khaydarian/spla/blog/2020-02-15-a.md

# 2020-02-15

Started experimenting with KiCad, and drew some partial crummy schematics.  For
now, I'm mostly duplicating what the HX8K dev board and FT2232HL datasheets
do, with some minor exceptions:  The FT2232HL datasheet recommends an LC
(inductor-capacitor) filter on the VPHY and VPLL inputs, to stabilize the PLL
-- but the HX8K dev board just has some decoupling capacitors, so that's maybe
sufficient.

The bigger problem here is part selection.  The big parts are kinda simple in
concept, but figuring out which exactly to choose is hard.  I don't have
constraints on cost -- the parts are cheap enough in single quantities -- but I
don't have good intuition on how hard it is to manually solder these things.
THT (Through-hole) is easy; surface-mount is trickier.  Nate mention that
0603-sized resistor/capacitor parts are doable manually, but smaller is a pain.
TFQP parts are probably ok, because I can just dump a bunch of flux and solder
on, and wick off the rest.  For BGA, it's hard to do without a solder-reflow
oven, which is probably too expensive to be worth it for a one-off ($250 - $450).

Sockets are annoying for QFP-100 (20x30x20x30), and are obsolete and pretty
much impossible to get.  I could build a breakout board for the PPU chips, at
the cost of chunky traces for the high(er) speed signals.  Not great.  Probably
it's better to just solder the things directly to the board, and hope not to
screw it up too many times.

Desoldering the PPU chips might be a huge pain, but that's something to
discover the hard way.

I also probably want to be able to control the CRAM / SPI EEPROM programming
mode electronically (ie, without swapping jumpers all the time), and to
control the power to the PPU chips as well.  For this stuff it's harmless to
have jumpers to configure manually as well; I'll need to actually decide this
stuff and write it down.

The SRAM in most FPGAs is registered, so probably I can't use it to replace
the VRAM chips.  On the other hand, I'll get these for free with the SNES's, so
maybe it's wise to just use them.  Possibly I'll also want to be able to drive
these directly, and hold the PPU chips in reset.
