khaydarian/spla/blog/2020-02-14-b.md

# 2020-02-14

Found a good example of KiCad projects for Gameboy hardware: https://github.com/Gekkio/gb-hardware
