khaydarian/spla/reference/SNES/links.md

# SNES Schematic

https://wiki.superfamicom.org/uploads/snes_schematic_color.pdf

# SNES Pinouts

https://wiki.superfamicom.org/schematics-ports-and-pinouts
https://gamesx.com/wiki/lib/exe/fetch.php?media=schematics:pinout_s-ppu1.pdf
https://gamesx.com/wiki/lib/exe/fetch.php?media=schematics:pinout_s-ppu2.pdf
