khaydarian/spla/software/color.h

// vi: ts=2:sw=2:sts=2:et

#ifndef COLOR_H
#define COLOR_H

#define ORIGIN "[H"
#define CLEARSCREEN "[2J"
#define CLEARLINE "[K"
#define BOLD "[1m"
#define GREEN "[92m"
#define RED "[91m"
#define BLUE "[94m"
#define RESET "[0m"

#endif
