khaydarian/spla/software/ftdi_list_devices.c

// vi: ts=2:sw=2:sts=2:et

#include <libusb.h>
#include <stdio.h>

#include "command.h"
#include "ftdi.h"
#include "ftdiutil.h"

// [Command]
// Description: Show all relevant devices connected by USB.
status ftdi_list_devices(int argc, char** argv) {
  RETURN_IF_ERROR(no_arguments(argc, argv));

  struct ftdi_device_list* devlist;
  int ret = ftdi_usb_find_all(ftdi, &devlist, 0, 0);
  if (ret < 0) {
    return ftdiutil_error("ftdi_usb_find_all", ret);
  }
  printf("Found %d FTDI device%s:\n", ret, (ret == 1 ? "" : "s"));

  char manufacturer[256];
  char description[256];
  char serial[256];

  int i = 0;
  for (struct ftdi_device_list* cur = devlist; cur; cur = cur->next, i++) {
    printf("Device #%d:\n", i);
    ret = ftdiutil_describe(ftdi, cur->dev, manufacturer, sizeof(manufacturer),
                            description, sizeof(description), serial,
                            sizeof(serial));
    if (ret < 0) {
      ftdi_list_free(&devlist);
      return ftdiutil_error("ftdi_usb_get_strings", ret);
    }
    printf("  Manufacturer: %s\n", manufacturer);
    printf("  Description:  %s\n", description);
    printf("  Serial:       %s\n", serial);
  }

  ftdi_list_free(&devlist);
  return OK;
}
